rowaaahmed/Smart-Home/solidworks/Elevator/final parts connected/final.SLDASM

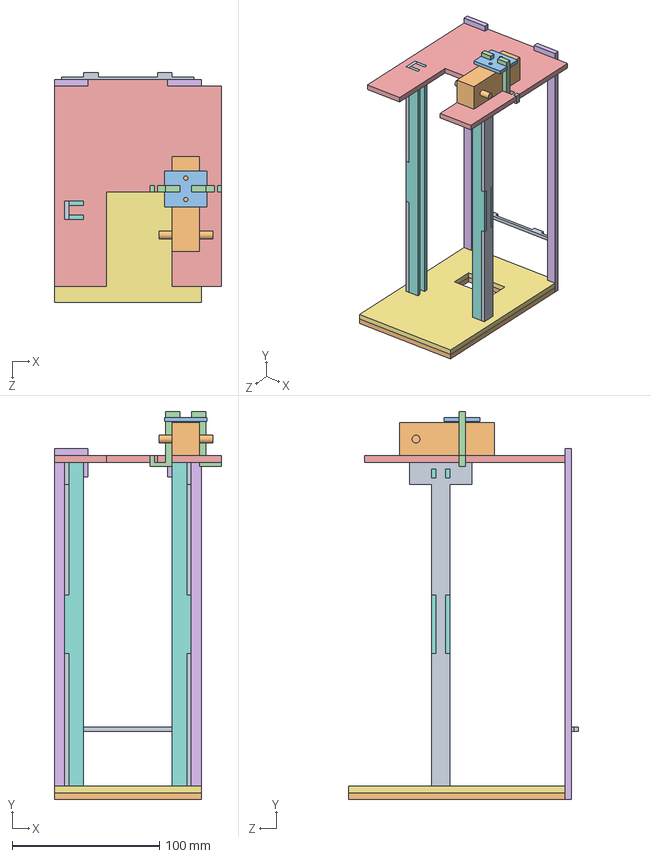
[picture p23: CAD file, 2025-08-05]
solidworks/Elevator/final parts connected/final.SLDASM
113.7 x 263.5 x 156.2 mm
base bottom
3amood el duide x 2
eli gmbo x 4
base top
4amood wara3
top
el bta3 da x 2
elzeft
motor
boundry
