rowaaahmed/Smart-Home/solidworks/solar tracker/Assem6.SLDASM

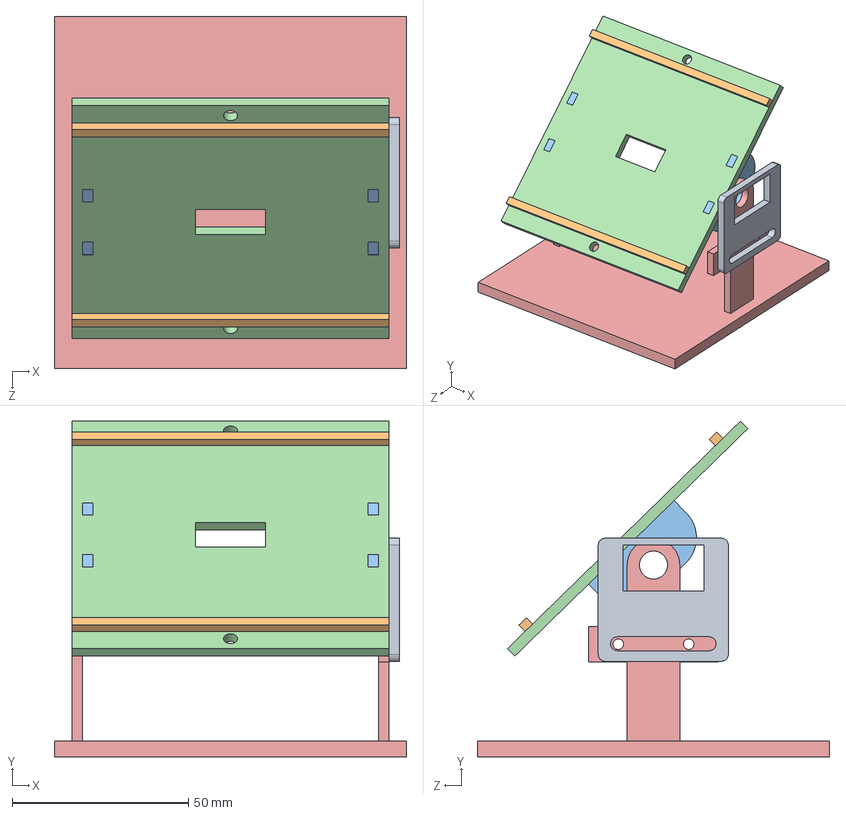
[picture p24: CAD file, 2025-08-05]
solidworks/solar tracker/Assem6.SLDASM
100.0 x 95.4 x 100.0 mm
stand
base
hole x 2
boundry x 2
bracket
