rowaaahmed/Smart-Home/solidworks/Elevator/elevator solid/Assem1.SLDASM

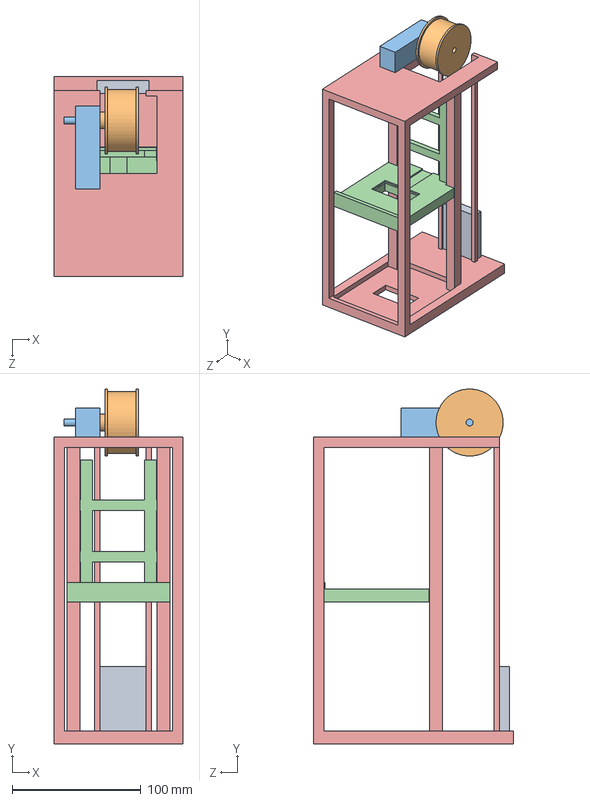
[picture p26: CAD file, 2025-08-05]
solidworks/Elevator/elevator solid/Assem1.SLDASM
100.0 x 275.2 x 155.0 mm
new guide
frame
motor
pulley
weight
