rowaaahmed/Smart-Home/solidworks/garage/garage solid/garage.SLDASM

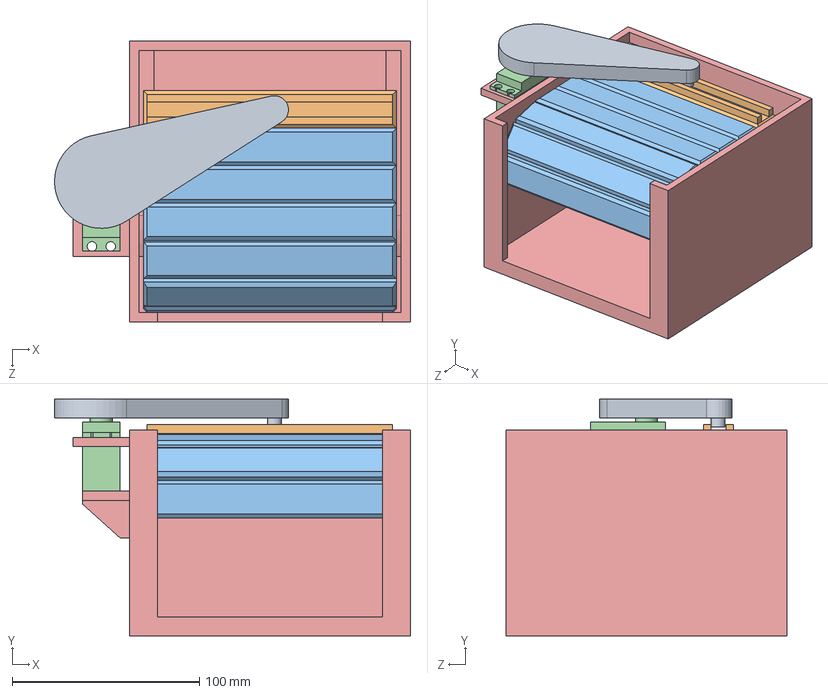
[picture p27: CAD file, 2025-08-05]
solidworks/garage/garage solid/garage.SLDASM
190.0 x 126.4 x 150.0 mm
garage part
servo
door segment x 6
last door segment 2
link 2
