rowaaahmed/Smart-Home/Autocad/Garage/garage 4.5mm.dxf

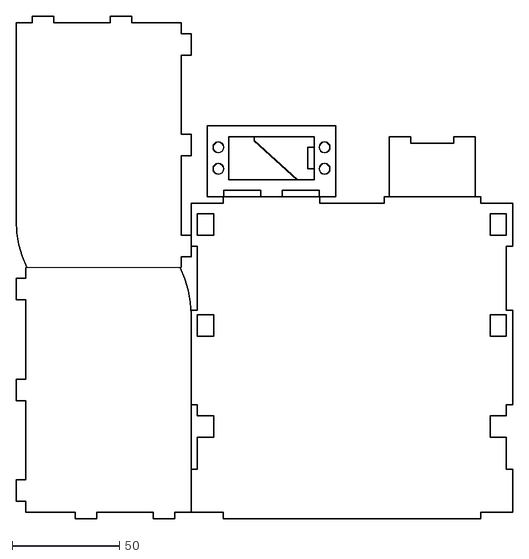
[picture p38: CAD file, 2025-08-05]
Autocad/Garage/garage 4.5mm.dxf
231.5 x 234.0
