rowaaahmed/Smart-Home/Autocad/Home parts/home parts final 3mm.dxf

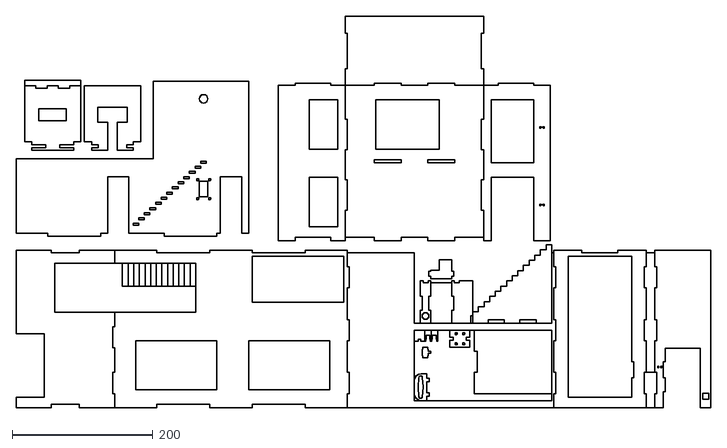
[picture p39: CAD file, 2025-08-05]
Autocad/Home parts/home parts final 3mm.dxf
986.0 x 555.1
