rowaaahmed/Smart-Home/Rack and pinion 3D printing/base gate.SLDPRT

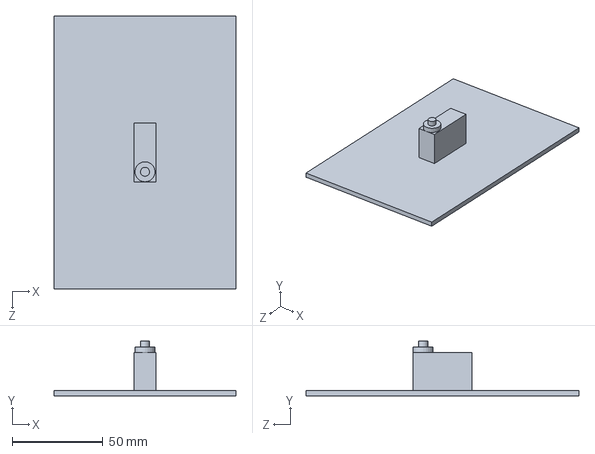
[picture p40: CAD file, 2025-08-05]
Rack and pinion 3D printing/base gate.SLDPRT
100.0 x 30.2 x 150.0 mm
