rowaaahmed/Smart-Home/solidworks/Elevator/elevator solid/pulley.SLDPRT

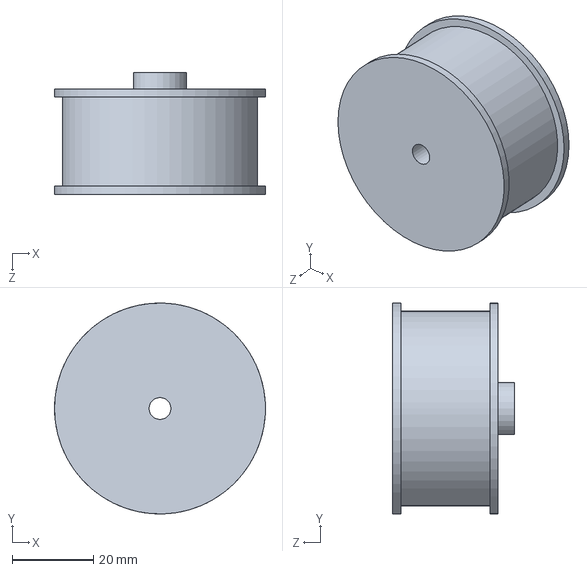
[picture p41: CAD file, 2025-08-05]
solidworks/Elevator/elevator solid/pulley.SLDPRT
52.0 x 52.0 x 30.0 mm
