rowaaahmed/Smart-Home/solidworks/Elevator/final parts connected/EL BTA3 EL TANI.SLDPRT

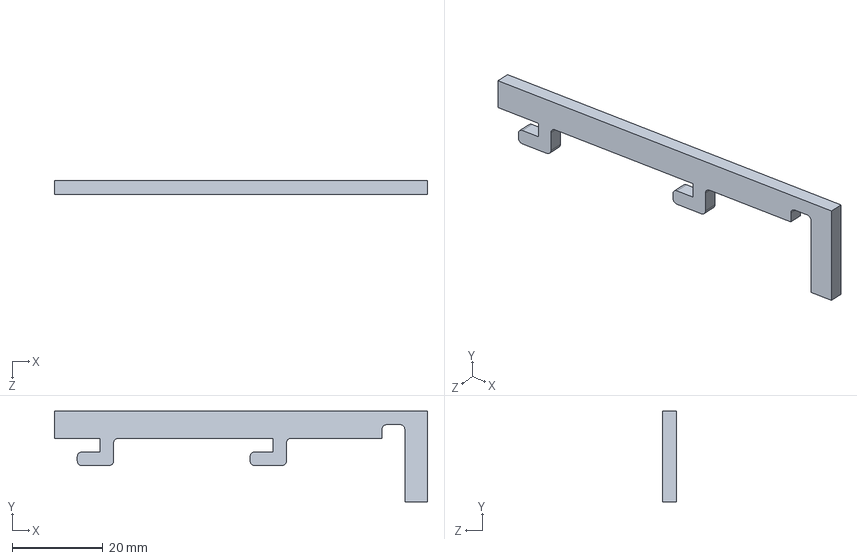
[picture p42: CAD file, 2025-08-05]
solidworks/Elevator/final parts connected/EL BTA3 EL TANI.SLDPRT
82.0 x 20.0 x 3.00 mm
