rowaaahmed/Smart-Home/solidworks/garage/garage solid/servo.SLDPRT

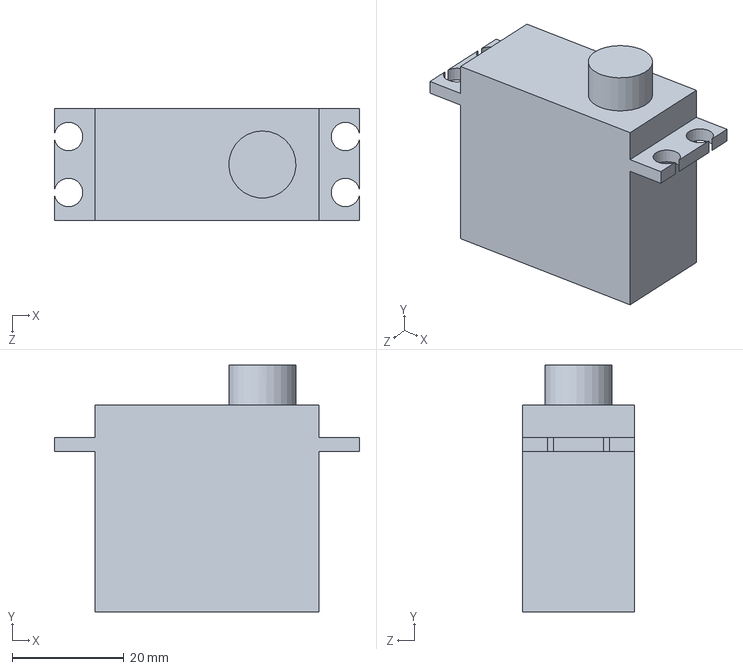
[picture p43: CAD file, 2025-08-05]
solidworks/garage/garage solid/servo.SLDPRT
54.5 x 44.1 x 20.0 mm
