rowaaahmed/Smart-Home/solidworks/solar tracker/stand.SLDPRT

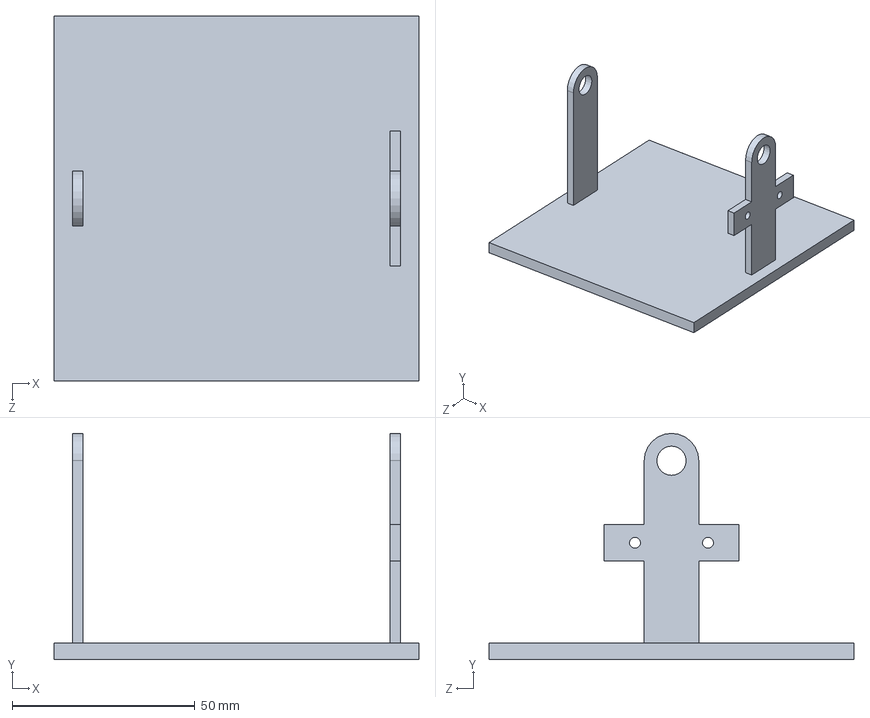
[picture p44: CAD file, 2025-08-05]
solidworks/solar tracker/stand.SLDPRT
100.0 x 62.0 x 100.0 mm
