rowaaahmed/Smart-Home/solidworks/Elevator/elevator solid/frame.SLDPRT

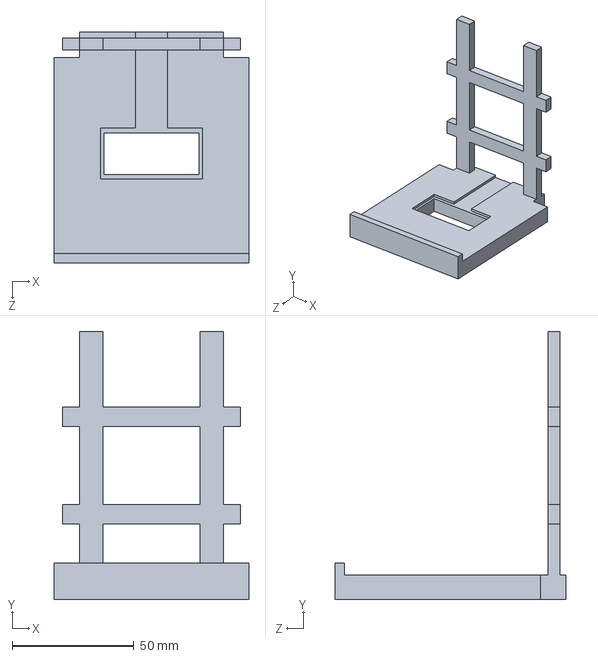
[picture p45: CAD file, 2025-08-05]
solidworks/Elevator/elevator solid/frame.SLDPRT
80.0 x 110.0 x 95.0 mm
