rowaaahmed/Smart-Home/solidworks/garage/garage solid/door segment.SLDPRT

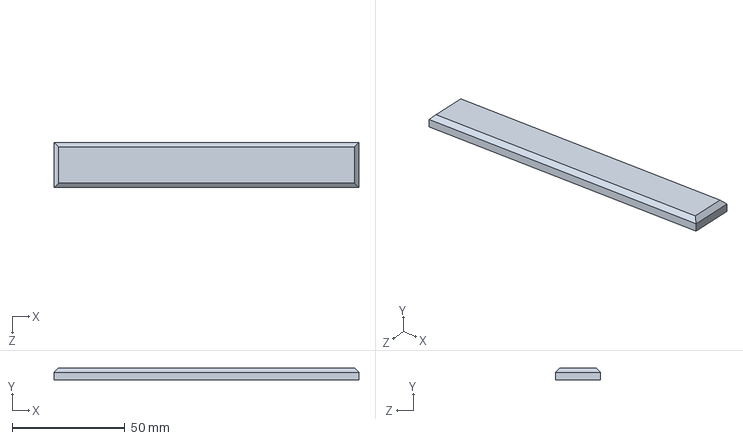
[picture p46: CAD file, 2025-08-05]
solidworks/garage/garage solid/door segment.SLDPRT
135.0 x 5.40 x 20.0 mm
