rowaaahmed/Smart-Home/solidworks/Home/block 2.SLDPRT

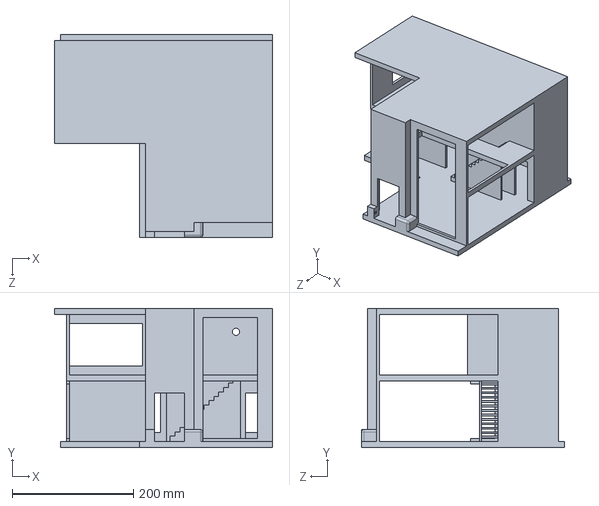
[picture p47: CAD file, 2025-08-05]
solidworks/Home/block 2.SLDPRT
360.0 x 230.0 x 335.0 mm
