rowaaahmed/Smart-Home/solidworks/Elevator/elevator solid/weight.SLDPRT

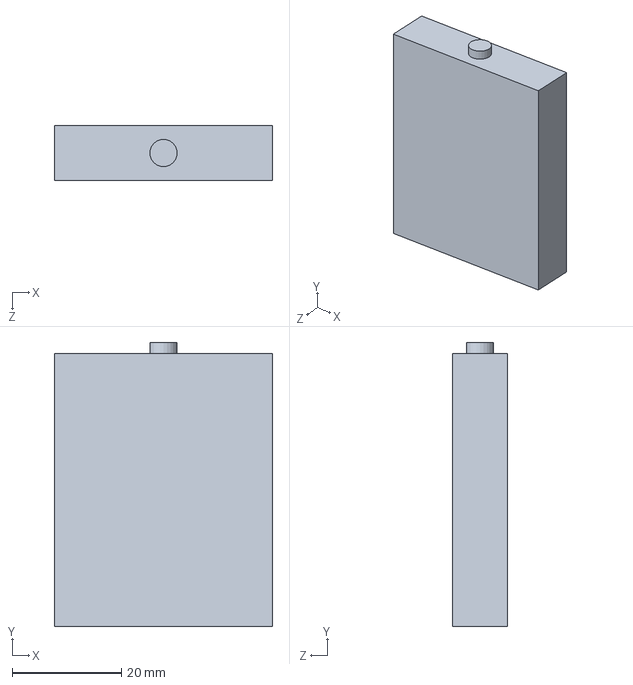
[picture p48: CAD file, 2025-08-05]
solidworks/Elevator/elevator solid/weight.SLDPRT
40.0 x 52.0 x 10.0 mm
