rowaaahmed/Smart-Home/solidworks/Elevator/final parts connected/eli gmbo.SLDPRT

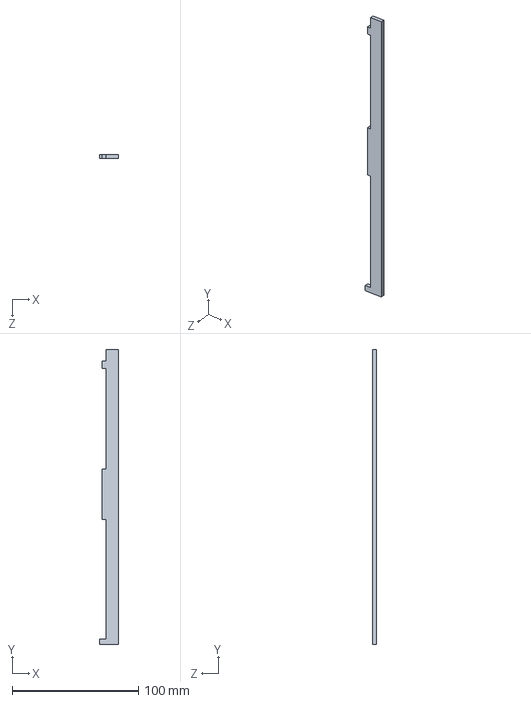
[picture p49: CAD file, 2025-08-05]
solidworks/Elevator/final parts connected/eli gmbo.SLDPRT
15.0 x 233.5 x 3.00 mm
