rowaaahmed/Smart-Home/solidworks/garage/garage solid/garage part.SLDPRT

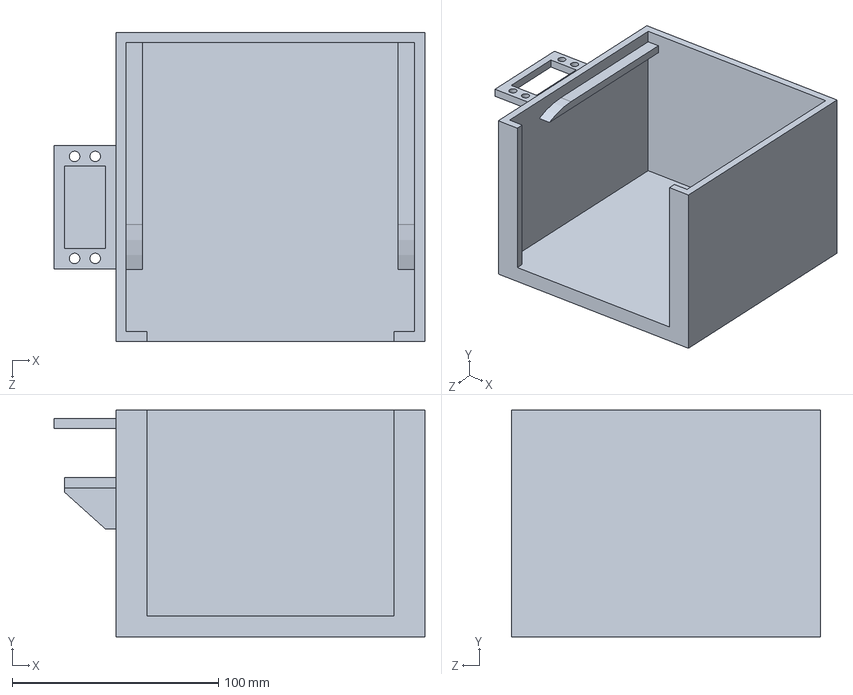
[picture p50: CAD file, 2025-08-05]
solidworks/garage/garage solid/garage part.SLDPRT
180.0 x 110.0 x 150.0 mm
