rowaaahmed/Smart-Home/solidworks/solar tracker/hole.SLDPRT

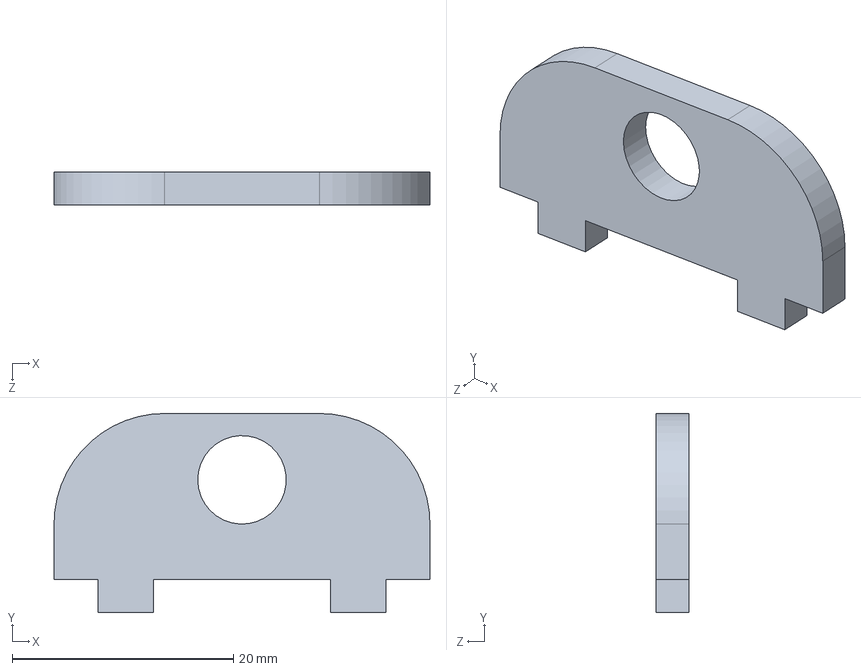
[picture p51: CAD file, 2025-08-05]
solidworks/solar tracker/hole.SLDPRT
34.0 x 18.0 x 3.00 mm
