rowaaahmed/Smart-Home/Rack and pinion 3D printing/newrack.STL

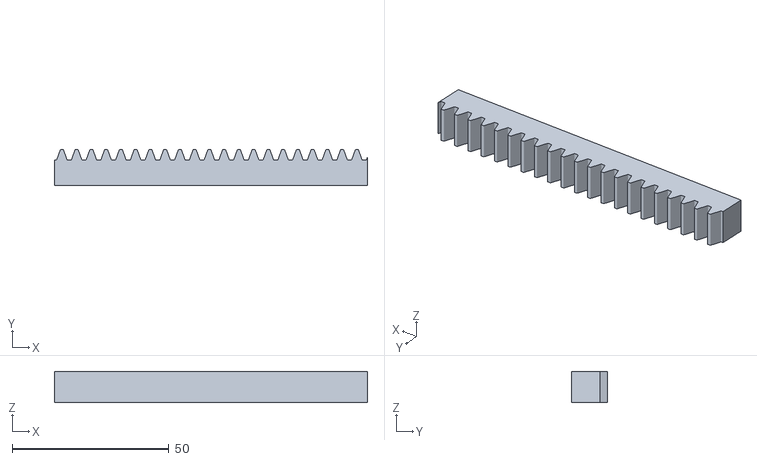
[picture p52: CAD file, 2025-08-05]
Rack and pinion 3D printing/newrack.STL
100.0 x 11.5 x 10.0
