rowaaahmed/Smart-Home/solidworks/Elevator/final parts connected/top.SLDPRT

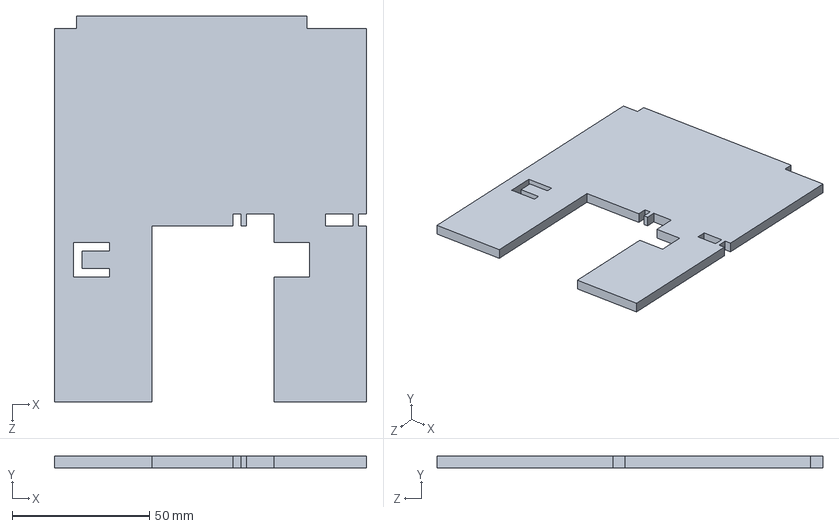
[picture p53: CAD file, 2025-08-05]
solidworks/Elevator/final parts connected/top.SLDPRT
113.7 x 4.50 x 140.5 mm
