rowaaahmed/Smart-Home/solidworks/solar tracker/base.SLDPRT

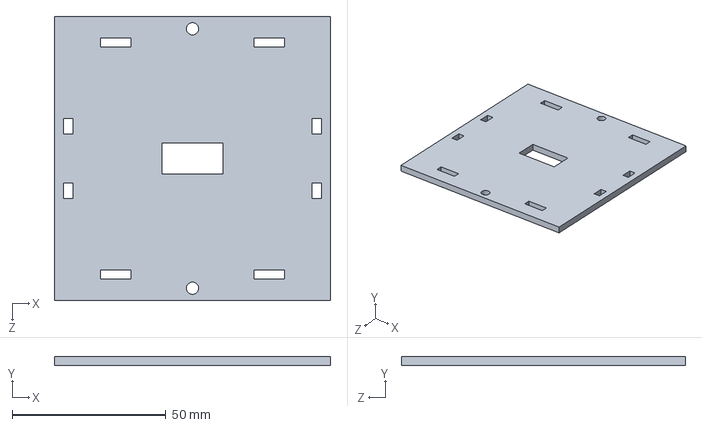
[picture p54: CAD file, 2025-08-05]
solidworks/solar tracker/base.SLDPRT
90.0 x 3.00 x 92.5 mm
