rowaaahmed/Smart-Home/Rack and pinion 3D printing/head servo.SLDPRT

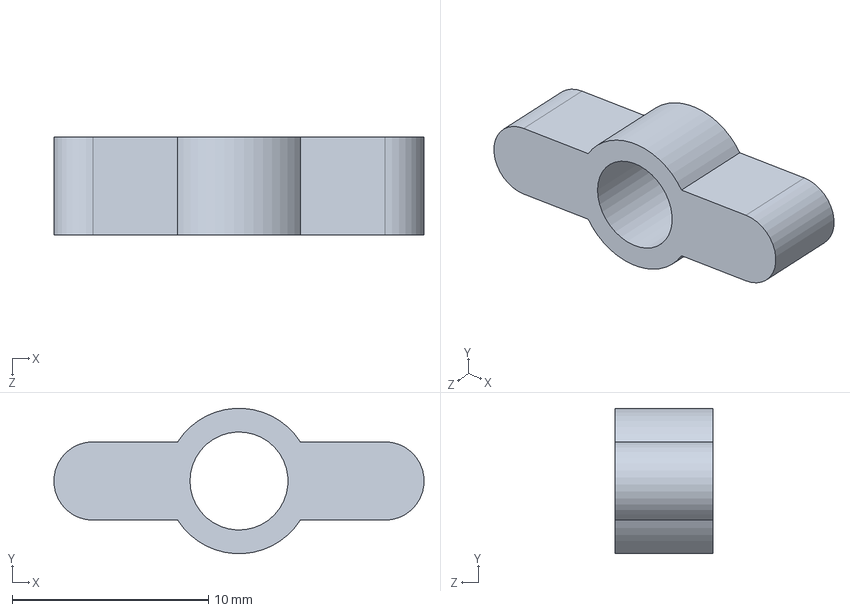
[picture p55: CAD file, 2025-08-05]
Rack and pinion 3D printing/head servo.SLDPRT
18.9 x 7.40 x 5.00 mm
