rowaaahmed/Smart-Home/solidworks/Elevator/elevator solid/motor.SLDPRT

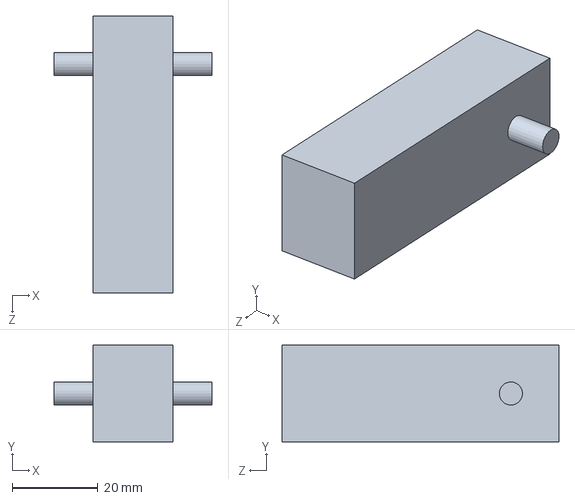
[picture p56: CAD file, 2025-08-05]
solidworks/Elevator/elevator solid/motor.SLDPRT
36.7 x 22.5 x 64.5 mm
