rowaaahmed/Smart-Home/solidworks/Elevator/final parts connected/el bta3 da.SLDPRT

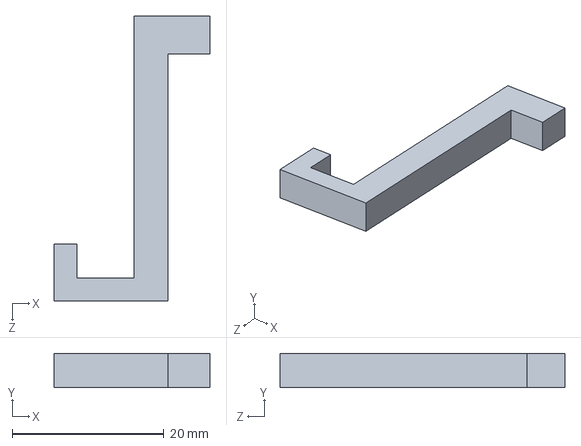
[picture p57: CAD file, 2025-08-05]
solidworks/Elevator/final parts connected/el bta3 da.SLDPRT
20.5 x 4.50 x 37.5 mm
