rowaaahmed/Smart-Home/solidworks/garage/garage solid/link 2.SLDPRT

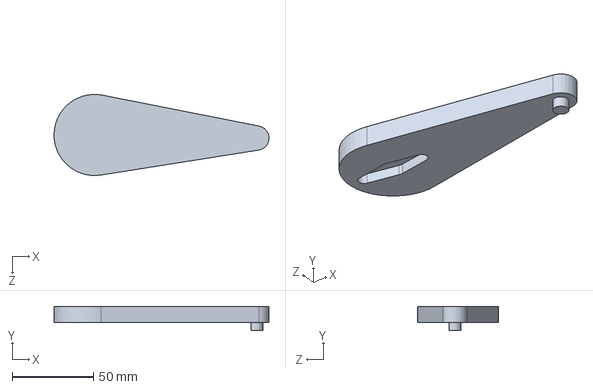
[picture p58: CAD file, 2025-08-05]
solidworks/garage/garage solid/link 2.SLDPRT
132.5 x 15.0 x 49.9 mm
