rowaaahmed/Smart-Home/solidworks/solar tracker/boundry.SLDPRT

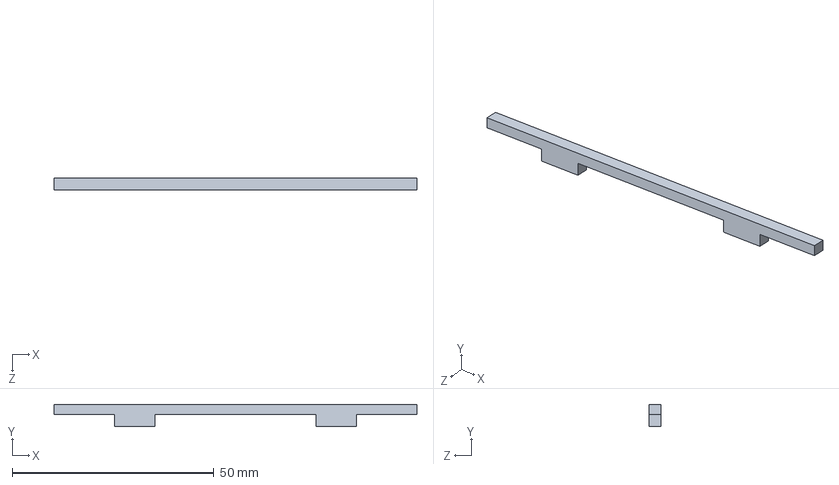
[picture p59: CAD file, 2025-08-05]
solidworks/solar tracker/boundry.SLDPRT
90.0 x 5.50 x 3.00 mm
