rowaaahmed/Smart-Home/Rack and pinion 3D printing/newgear.SLDPRT

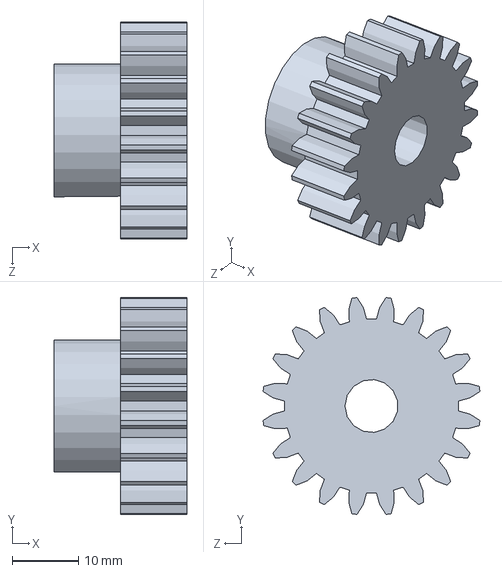
[picture p60: CAD file, 2025-08-05]
Rack and pinion 3D printing/newgear.SLDPRT
20.0 x 32.7 x 32.7 mm
