rowaaahmed/Smart-Home/solidworks/Elevator/final parts connected/4amood wara3.SLDPRT

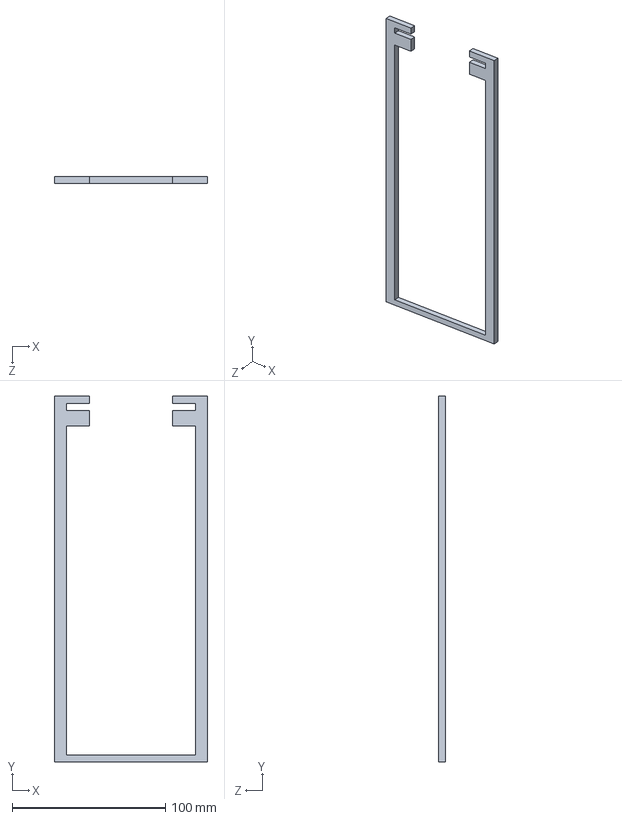
[picture p61: CAD file, 2025-08-05]
solidworks/Elevator/final parts connected/4amood wara3.SLDPRT
100.0 x 238.5 x 4.50 mm
