rowaaahmed/Smart-Home/solidworks/Elevator/final parts connected/3amood el duide.SLDPRT

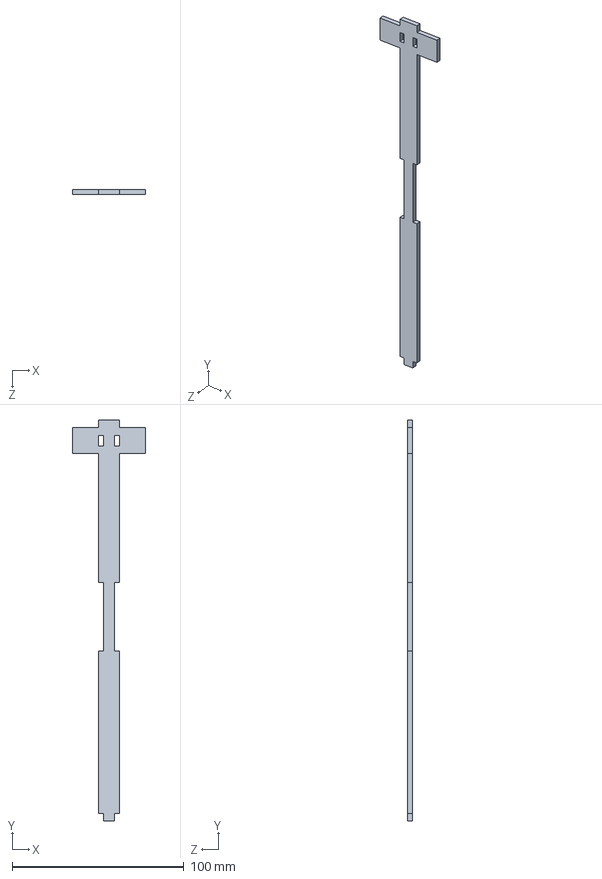
[picture p62: CAD file, 2025-08-05]
solidworks/Elevator/final parts connected/3amood el duide.SLDPRT
42.5 x 233.5 x 3.00 mm
