rowaaahmed/Smart-Home/solidworks/Elevator/final parts connected/base top.SLDPRT

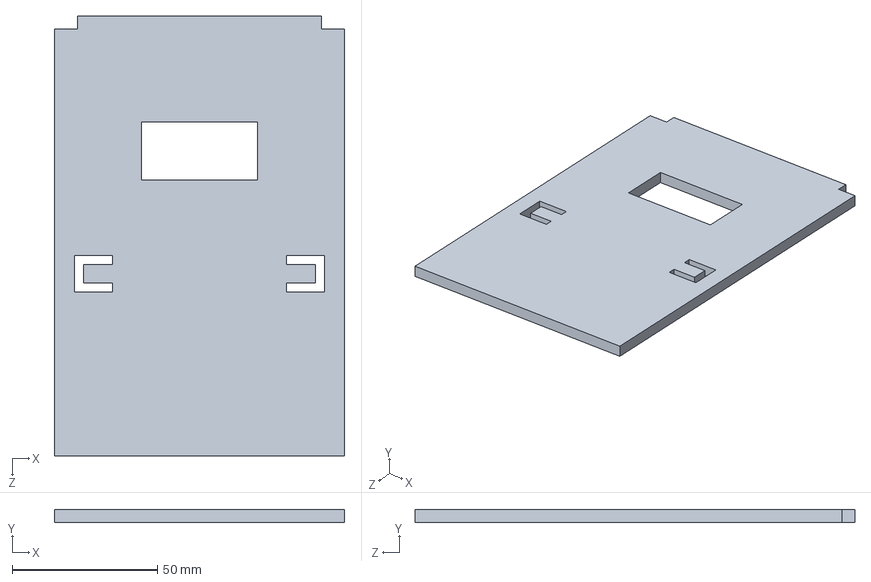
[picture p63: CAD file, 2025-08-05]
solidworks/Elevator/final parts connected/base top.SLDPRT
100.0 x 4.50 x 151.5 mm
