rowaaahmed/Smart-Home/solidworks/Elevator/final parts connected/elzeft.SLDPRT

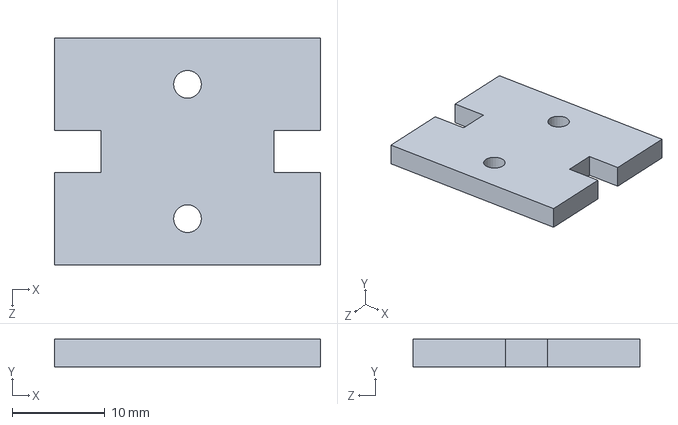
[picture p64: CAD file, 2025-08-05]
solidworks/Elevator/final parts connected/elzeft.SLDPRT
28.7 x 3.00 x 24.5 mm
